todbot/macropadsynthplug/circuitpython/drum_machine/drum_patterns.py

# drum_patterns.py --
# data for drums pattern
# part of MacroPadSynthPlug project: https://github.com/todbot/macropadsynthplug
# 29 Dec 2022 - @todbot / Tod Kurt



patterns_demo = [
    {
        'name': 'patt0',
        'len': 32,
        'base': [
            # steps      11 1111  1111 2222 2222 2233
            #0123 4567 8901 2345  6789 0123 4567 8901
            '1000 1000 1000 1000  1000 1000 1000 1000', # bd
            '0000 0000 1000 0000  0000 0000 1000 0000', # sd
            '0000 1000 0000 1000  0000 1000 0000 1000', # oh
            '0000 0000 0000 0000  0000 0000 0000 0010', # ch

            '0000 0000 0000 0000  0000 0000 0000 0000', # cl
            '0000 0000 0000 0000  0000 0000 0000 0000', # tm
            '0000 0000 0000 0000  0000 0000 0000 0000', # cw
            '0000 0000 0000 0000  0000 0000 0000 0000', # cy
        ],
    },
    {
        'name': 'patt1',
        'len': 32,
        'base': [
            # steps      11 1111  1111 2222 2222 2233
            #0123 4567 8901 2345  6789 0123 4567 8901
            '1000 0000 1000 0000  1000 0000 1000 0000', # bd
            '0000 0000 1000 0000  0000 0000 1000 0000', # sd
            '0010 0010 0010 0010  0010 0010 0010 0000', # oh
            '0000 0000 0000 0000  0000 0000 0000 0010', # ch

            '0000 0000 0000 0000  0000 0000 0000 0000', # cl
            '0000 0000 0000 0000  0000 0000 0000 0000', # tm
            '0000 0000 0000 0000  0000 0001 0001 0000', # cw
            '0000 0000 0000 0000  0000 0000 0000 0010', # cy
        ],
    },
    {
        'name': 'rock1a',
        'len': 32,
        'base': [
            # steps      11 1111  1111 2222 2222 2233
            #0123 4567 8901 2345  6789 0123 4567 8901
            '1000 0000 1000 1000  1000 0000 1000 0000', # bd
            '0000 1000 1000 1000  0000 1000 0000 1000', # sd
            '1010 1010 1010 1010  1010 1010 1010 1000', # oh
            '0000 0000 0000 0000  0000 0000 0000 0010', # ch

            '0000 0000 0000 0000  0000 0000 0000 0000', # cl
            '0000 0000 0000 0000  0000 0000 0000 0000', # tm
            '0000 0000 0000 0000  0000 0001 0001 0000', # cw
            '0000 0000 0000 0000  0000 0000 0000 0010', # cy
        ],
    },
]
